paulgrammy/Bachelor-Thesis/doc/circuit_levelshifter&mux.png

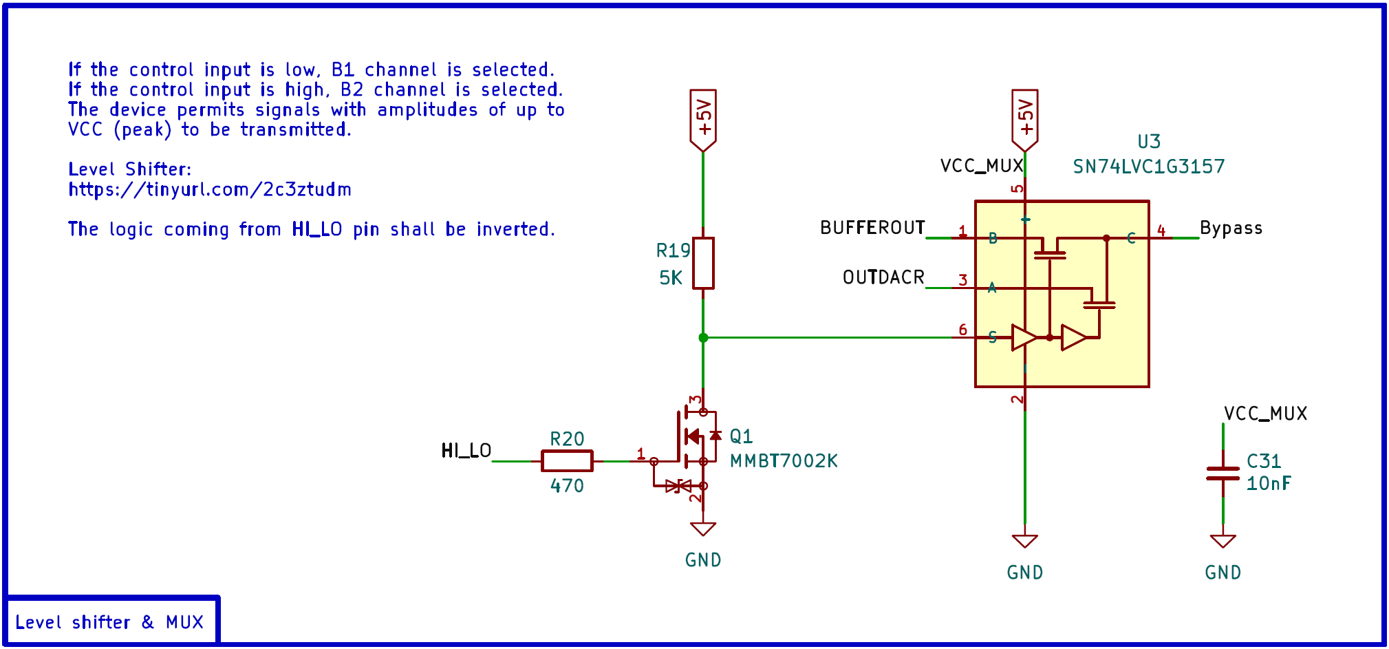
doc/circuit_levelshifter&mux.png
