paulgrammy/Bachelor-Thesis/doc/circuit_status.png

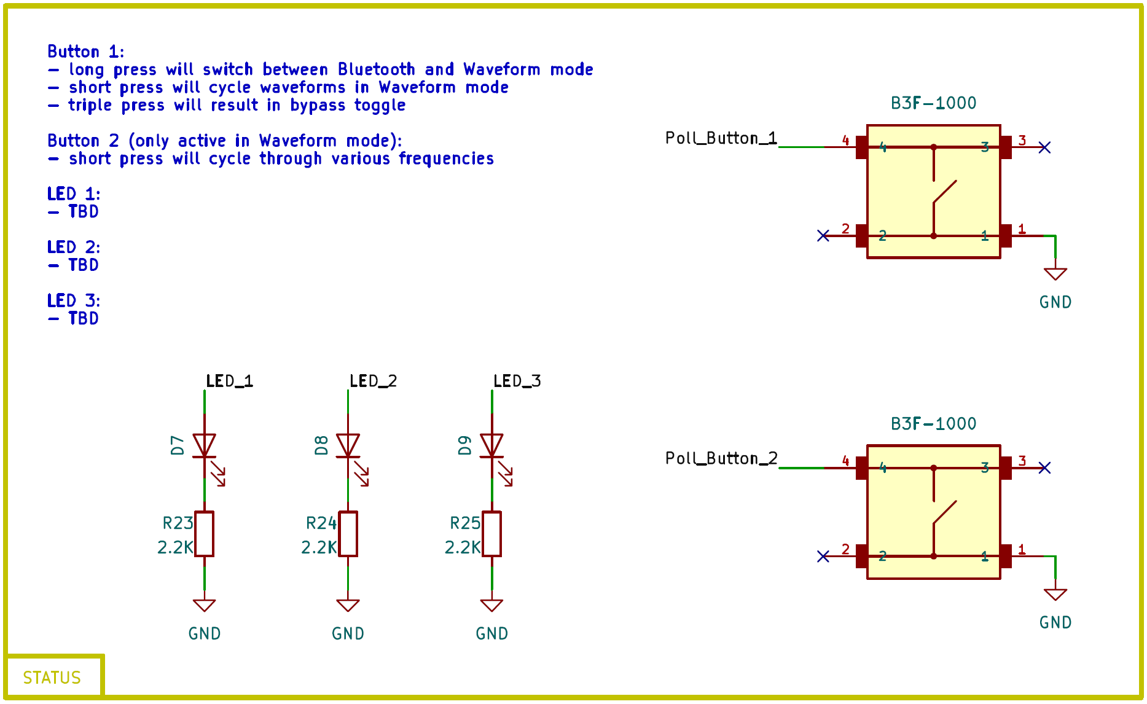
doc/circuit_status.png
