paulgrammy/Bachelor-Thesis/doc/circuit_voltagedivider.png

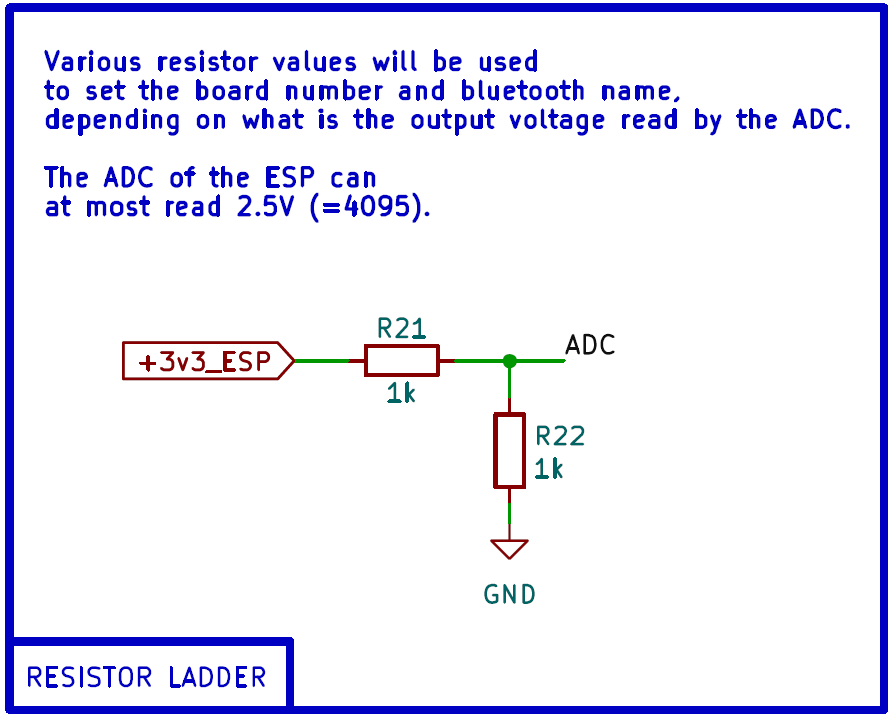
doc/circuit_voltagedivider.png
