paulgrammy/Bachelor-Thesis/doc/I2S Philips Standard.png

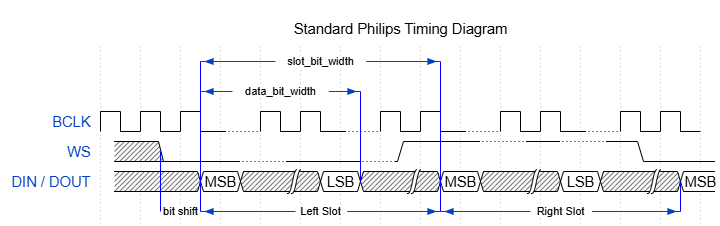
doc/I2S Philips Standard.png
