paulgrammy/Bachelor-Thesis/doc/PCB__IRL.jpg

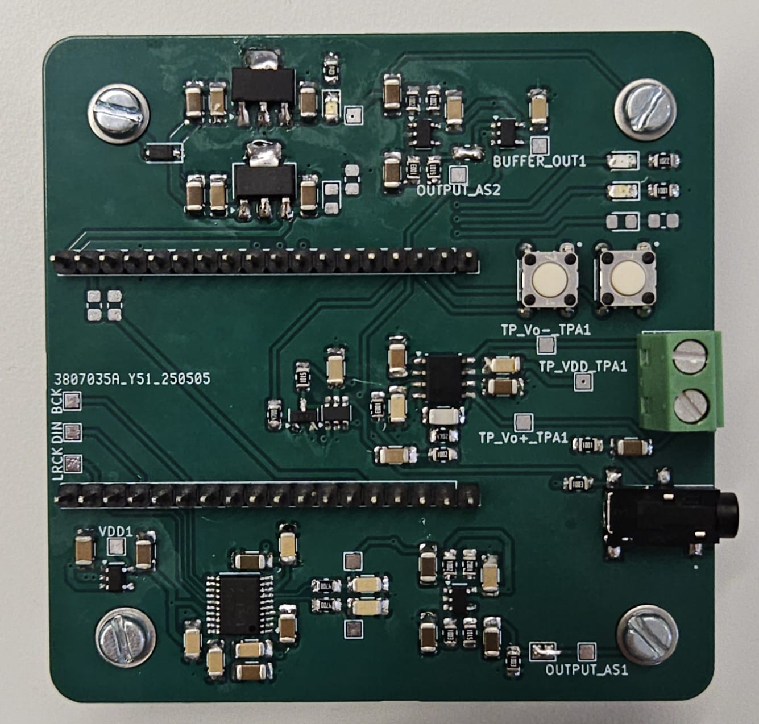
doc/PCB__IRL.jpg
