paulgrammy/Bachelor-Thesis/doc/Sound_EQ_View.png

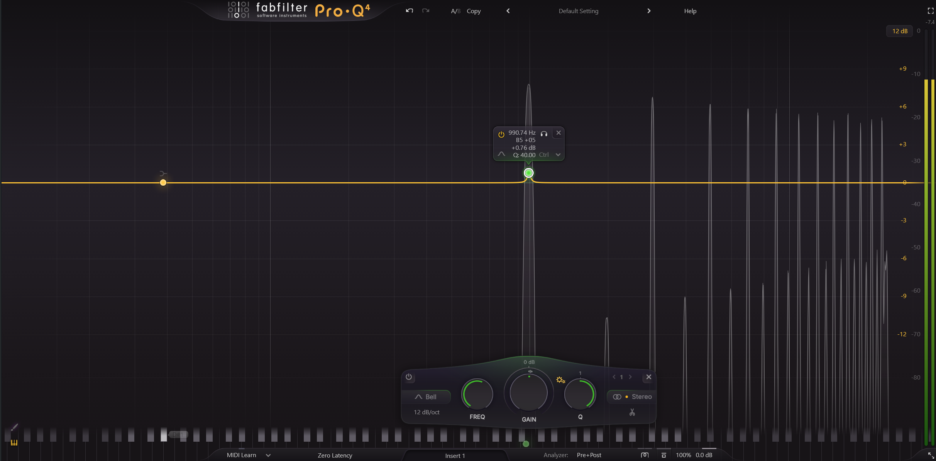
doc/Sound_EQ_View.png
