paulgrammy/Bachelor-Thesis/doc/Sound_OSC_View.png

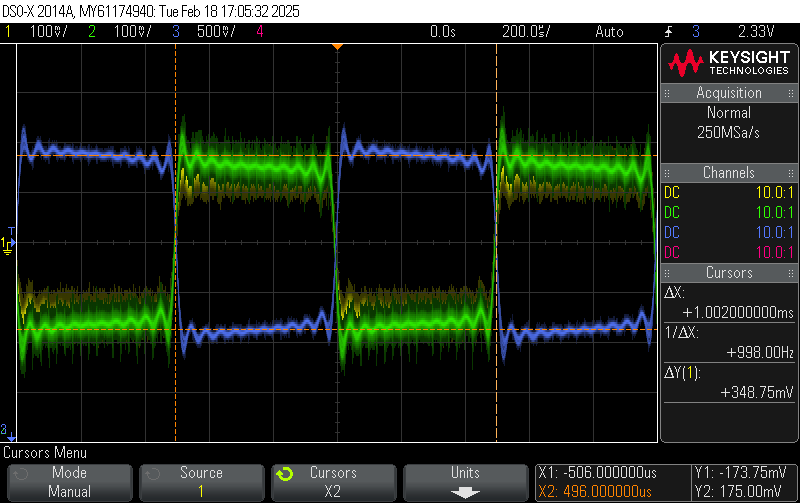
doc/Sound_OSC_View.png
