paulgrammy/Bachelor-Thesis/doc/Studienarbeit_Blockdiagram.png

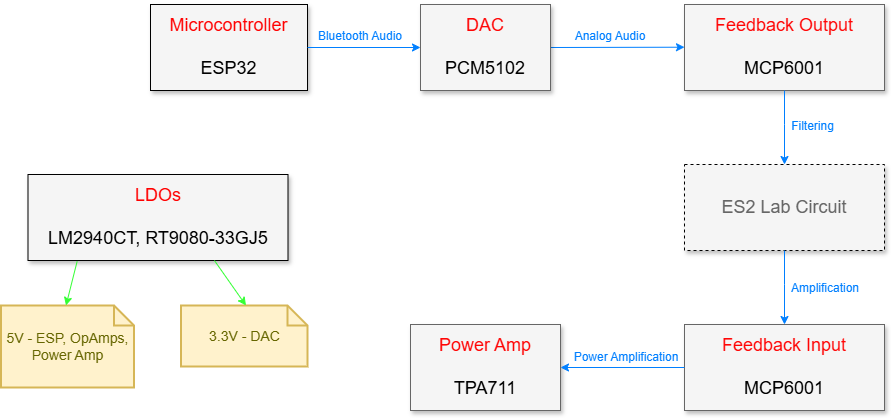
doc/Studienarbeit_Blockdiagram.png
