paulgrammy/Bachelor-Thesis/doc/Studienarbeit_PCB_3D.png

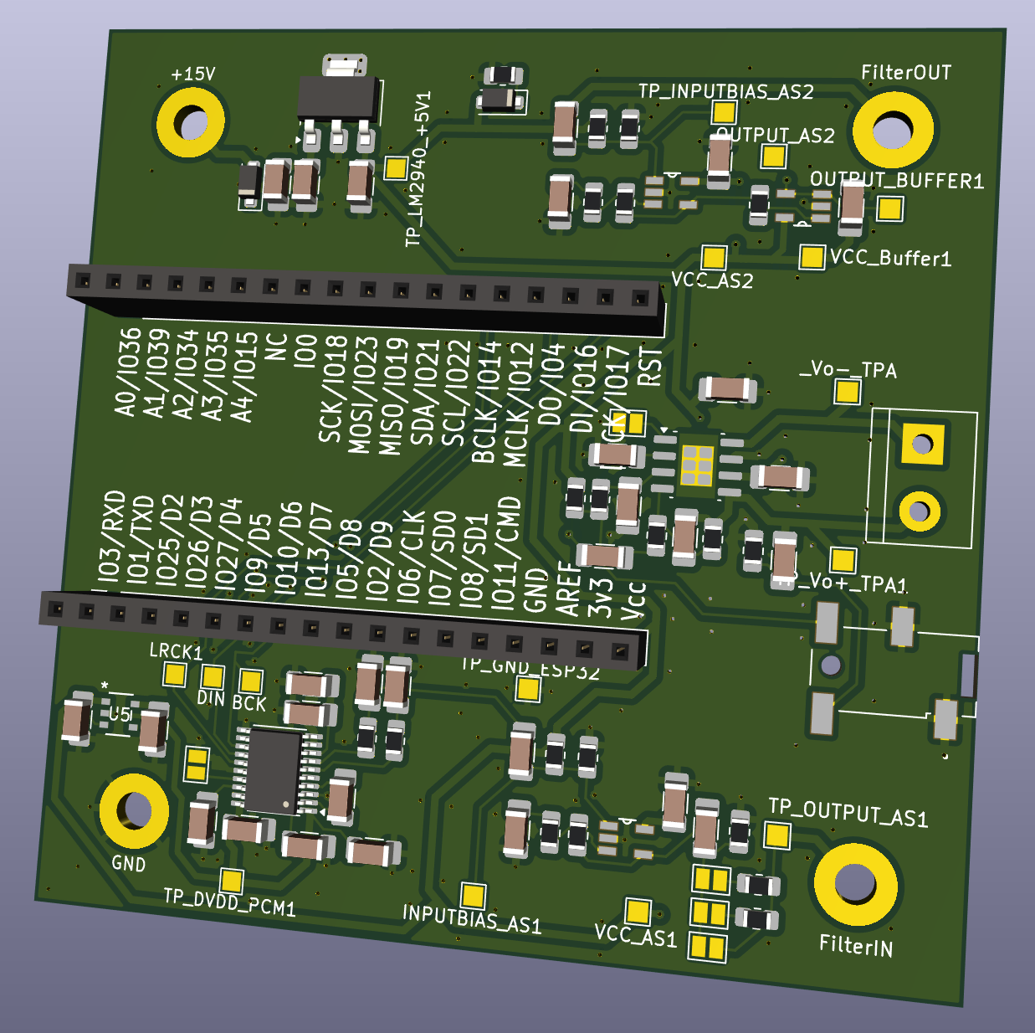
doc/Studienarbeit_PCB_3D.png
