paulgrammy/Bachelor-Thesis/schematics/ltspice/Student Research.asc

C1: cap; {C}
C2: cap; {C}
C3: cap; {C}
C4: cap; {C}
C6: cap; 10µF
R1: res; 100k
R2: res; 10k
R3: res; 10k
R4: res; 10k
R5: res; 10k
R6: res; 10k
R7: res; 1k
RF1: res; 5k
RF2: res; 5k
RG1: res; 100k
RG2: res; 100k
U1: MCP6001
U2: MCP6001
U3: MCP6001
V1: voltage; 5
V3: voltage; SINE(0 150m 2.5k); AC 1
Named nets: 0, 5V, IC, ES2_Filter, Vin, Vout
.ac dec 20 1 100k
.inc MCP6001.lib
.param C=10uF
.ac dec 20 1 1Meg
Power Supply
Extras
Simulations
Formulas
Vout = Vin * [(RF + RG)/RG] + (Vcc/2) * [(RF+RG)/RG]
.ic V(IC) = 0
;.options ptrantau=1u
;.option cshunt=1e-12
;.option gmin=1e-10 abstol=1e-10 reltol=0.003
.tran 0 50ms 0 200
